nathanjds001/fdspapr/src/cad_pictures/Filter Cap.jpg

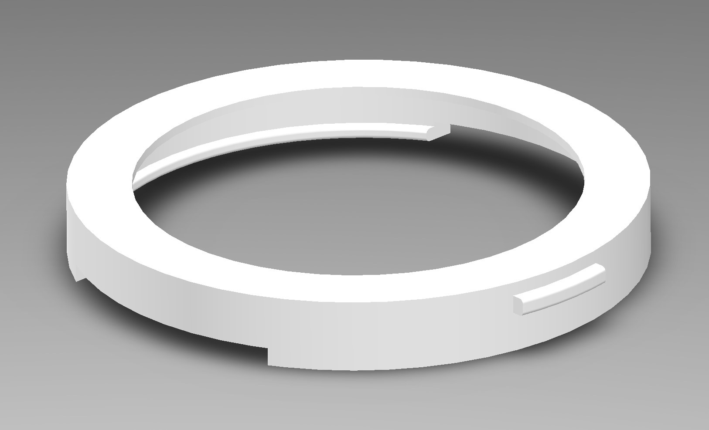
src/cad_pictures/Filter Cap.jpg
