nathanjds001/fdspapr/src/cad_pictures/Filter ring.jpg

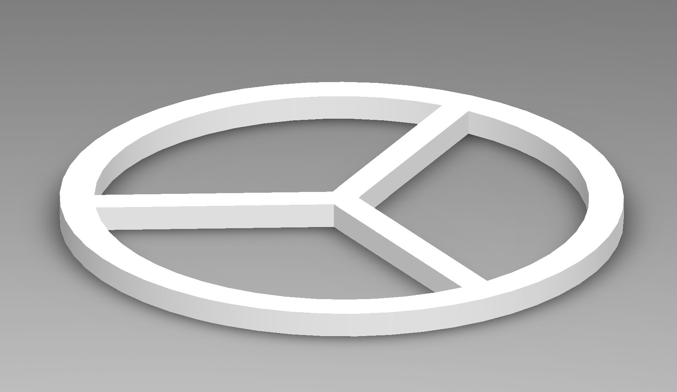
src/cad_pictures/Filter ring.jpg
