nathanjds001/fdspapr/src/cad_pictures/Housing.jpg

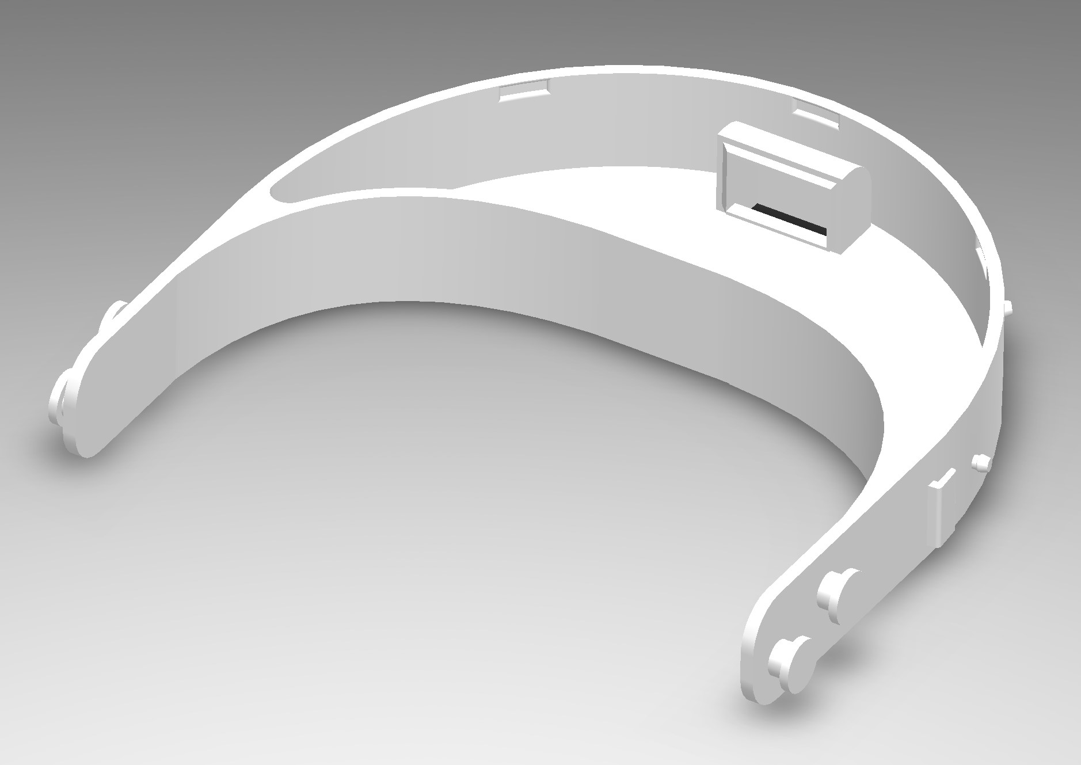
src/cad_pictures/Housing.jpg
