nathanjds001/fdspapr/src/cad_pictures/Lid.jpg

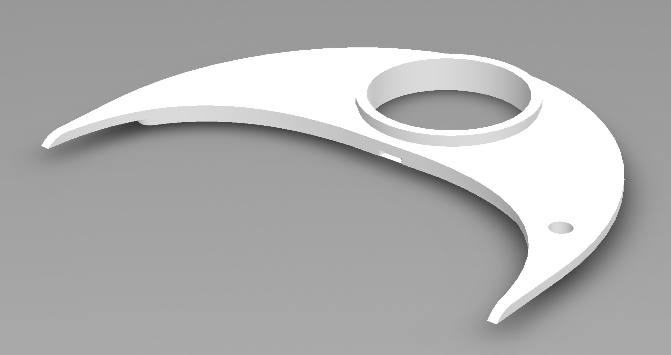
src/cad_pictures/Lid.jpg
