nathanjds001/fdspapr/src/cad_pictures/Vent bottom.jpg

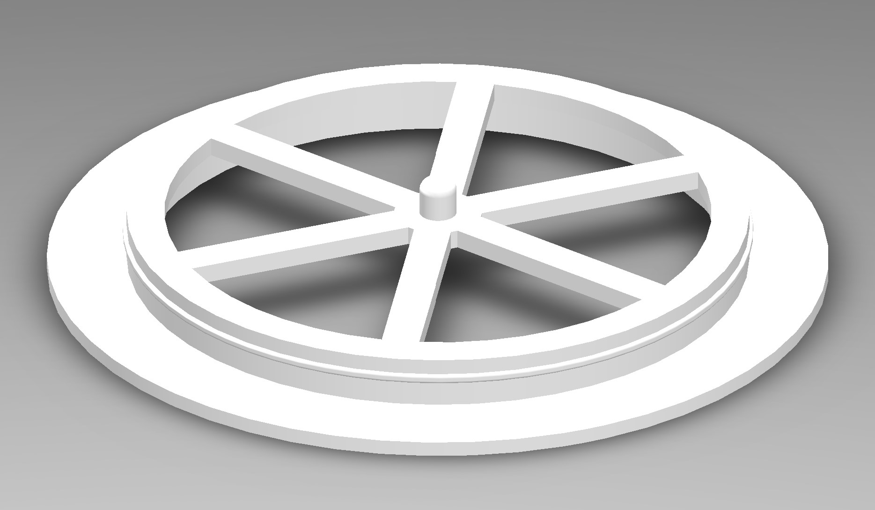
src/cad_pictures/Vent bottom.jpg
