nathanjds001/fdspapr/src/cad_pictures/Vent top.jpg

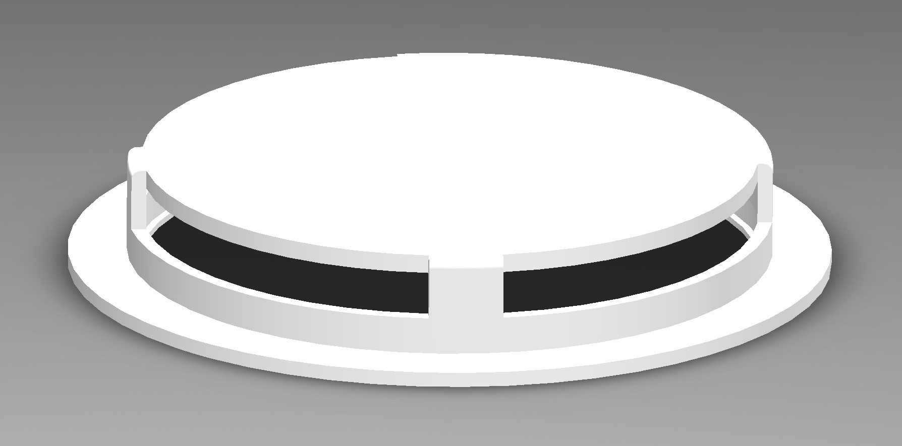
src/cad_pictures/Vent top.jpg
