nathanjds001/fdspapr/src/instructables_pictures/0.3 Components - Labelled.png

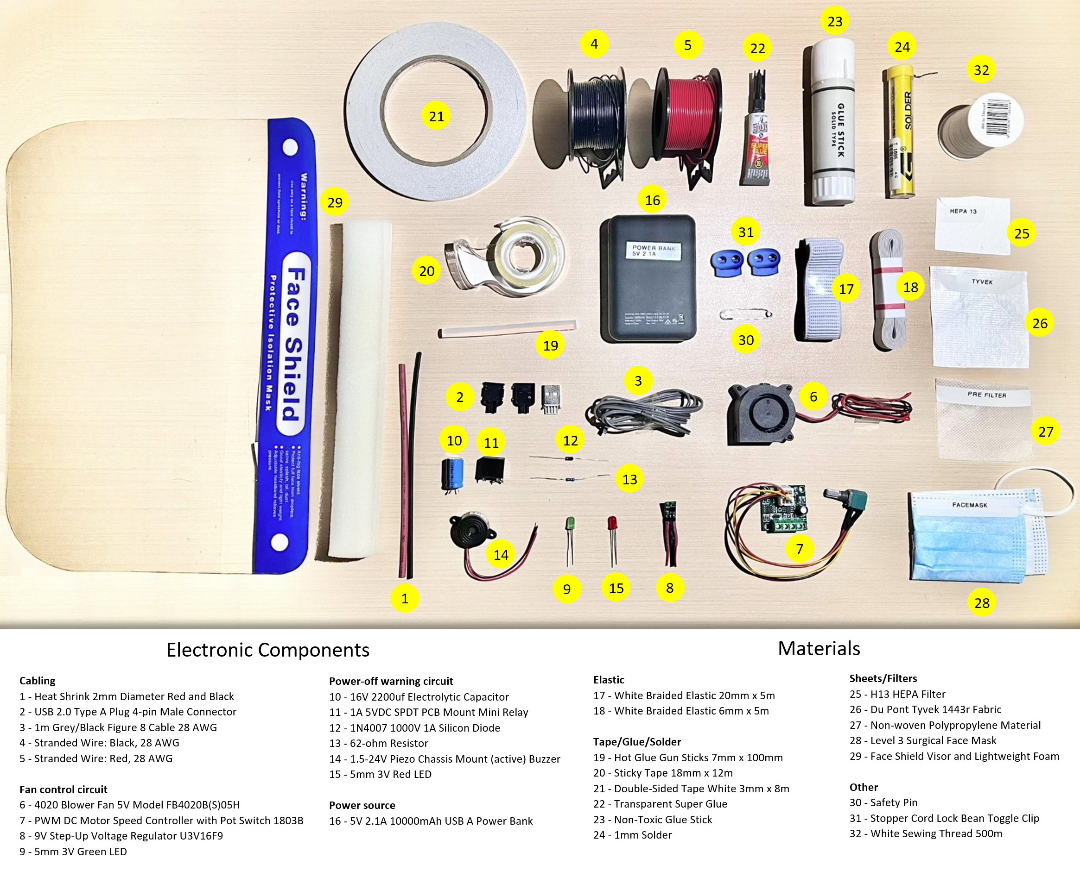
src/instructables_pictures/0.3 Components - Labelled.png
