nathanjds001/fdspapr/src/instructables_pictures/0.3 Components.jpg

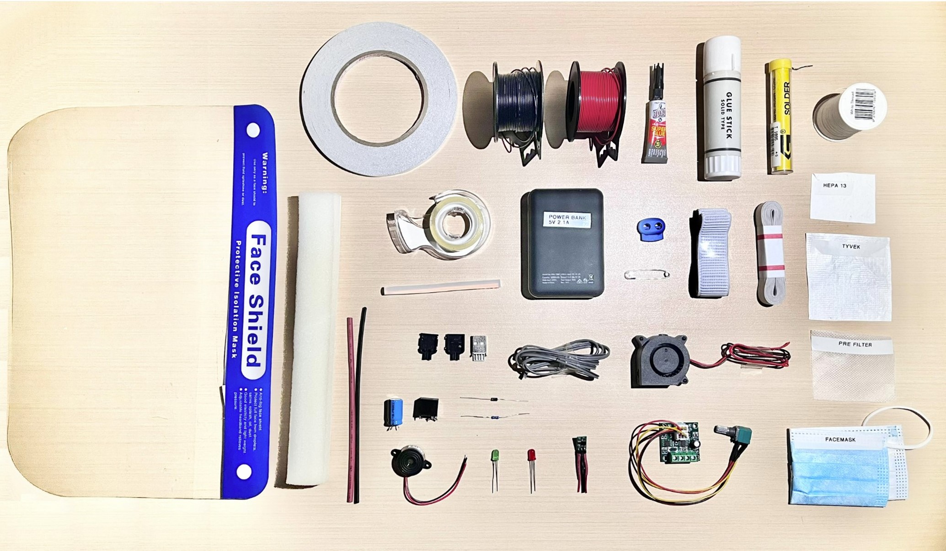
src/instructables_pictures/0.3 Components.jpg
