nathanjds001/fdspapr/src/instructables_pictures/1.2 3D Parts.jpg

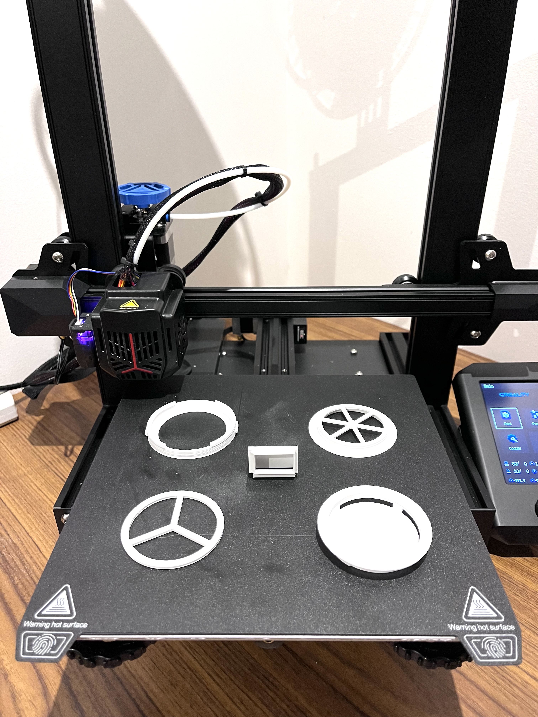
src/instructables_pictures/1.2 3D Parts.jpg
