nathanjds001/fdspapr/src/cad/Solidworks_Files/1. Face Shield Assembly.SLDASM

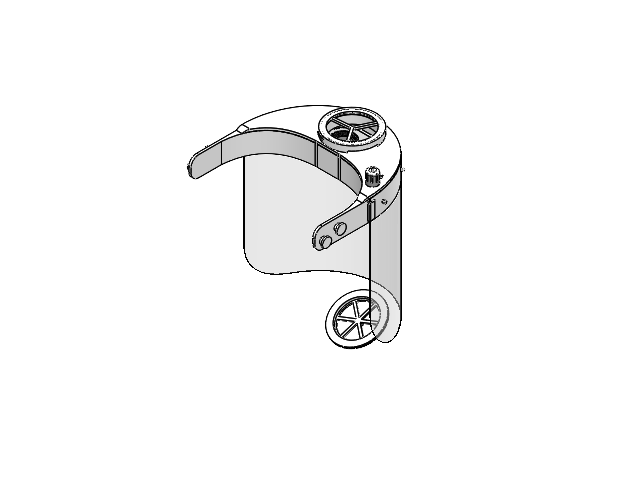
[picture p82: CAD file, 2024-04-08]
src/cad/Solidworks_Files/1. Face Shield Assembly.SLDASM
Vent bottom
Vent top
Housing
Plastic Shield
Lid
LED_D5.0mm_CLEAR x 2
4020 Blower Fan
Filter cap
Filter ring
Pot
4020 Blower Fan Funnel
Pot knob
