nathanjds001/fdspapr/src/cad_pictures/Assembly exploded view screenshot.jpg

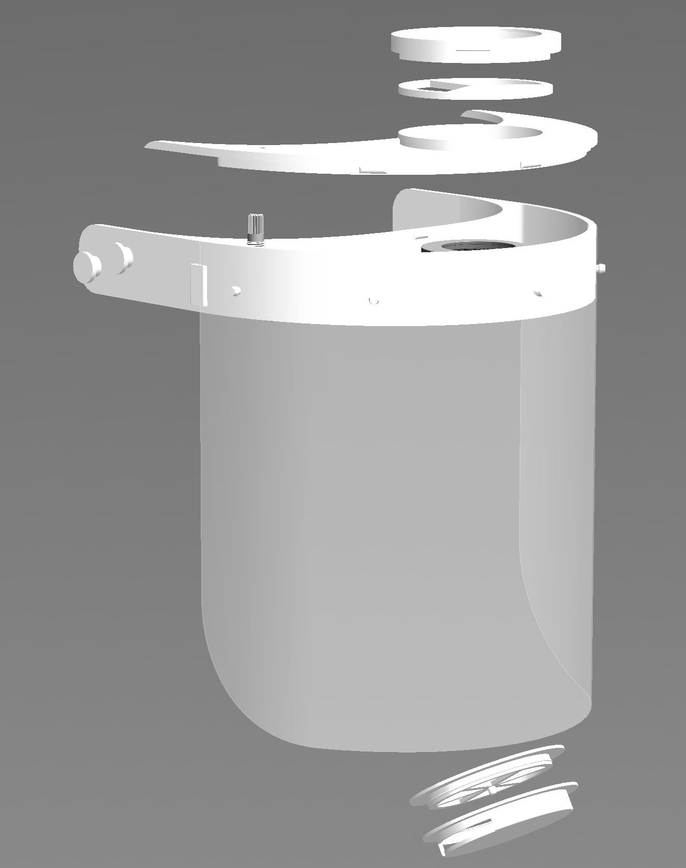
src/cad_pictures/Assembly exploded view screenshot.jpg
