nathanjds001/fdspapr/src/cad_pictures/Assembly Screenshot white bg 2.jpg

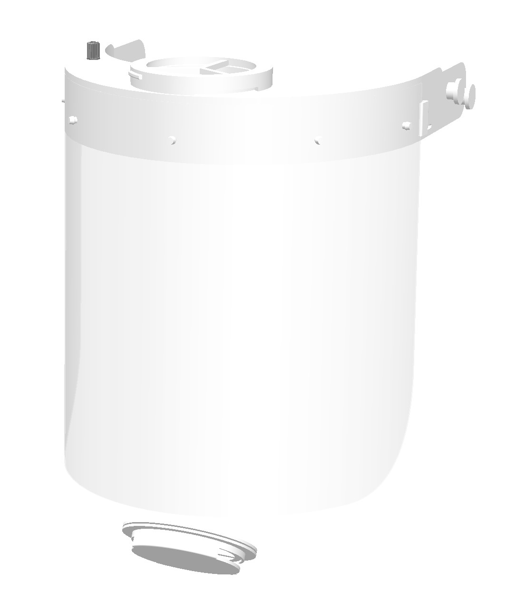
src/cad_pictures/Assembly Screenshot white bg 2.jpg
