nathanjds001/fdspapr/src/cad_pictures/Assembly Screenshot white bg.jpg

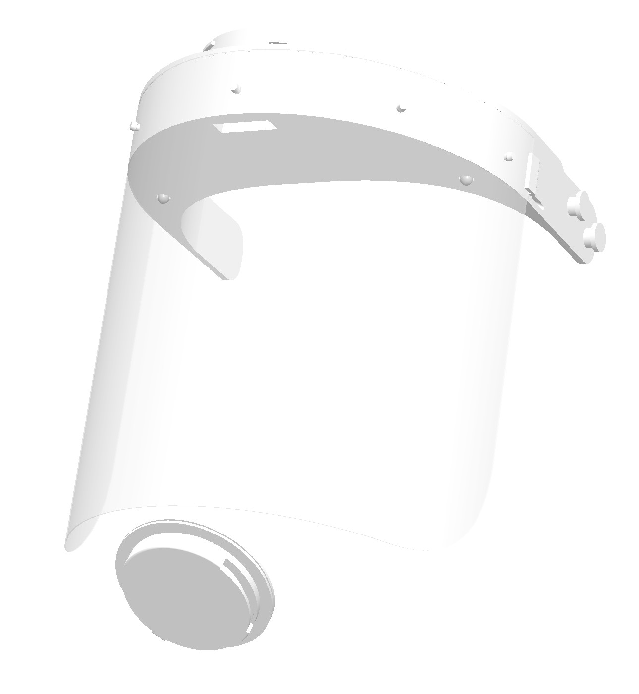
src/cad_pictures/Assembly Screenshot white bg.jpg
