nathanjds001/fdspapr/src/cad_pictures/Assembly screenshot.jpg

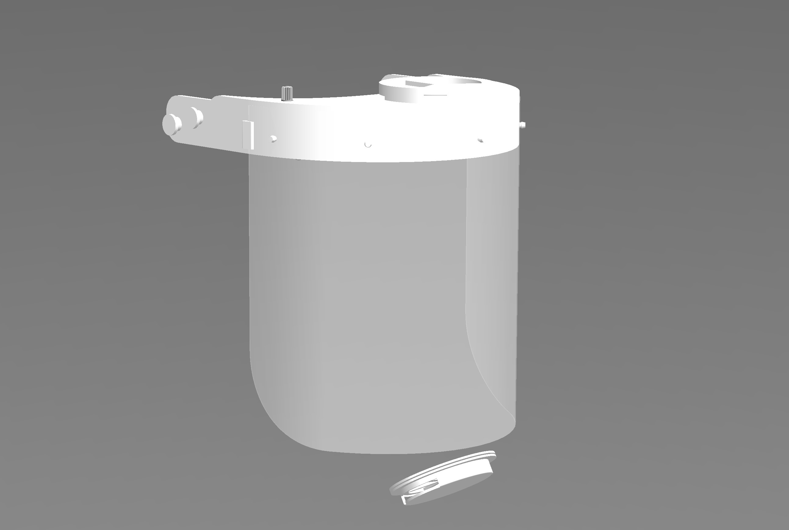
src/cad_pictures/Assembly screenshot.jpg
