nathanjds001/fdspapr/src/instructables_pictures/0.1 Full PAPR.png

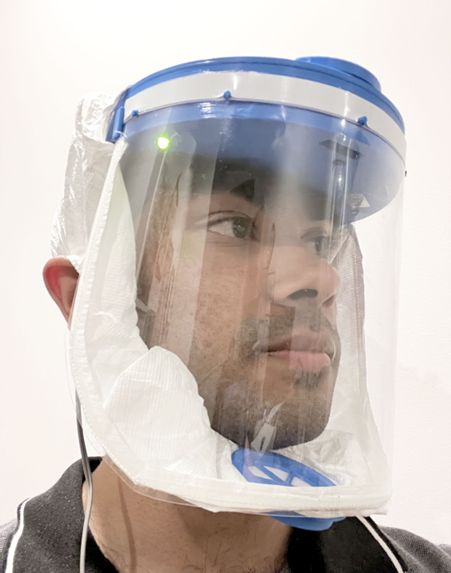
src/instructables_pictures/0.1 Full PAPR.png
