nathanjds001/fdspapr/src/instructables_pictures/0.2 Simple PAPR.jpg

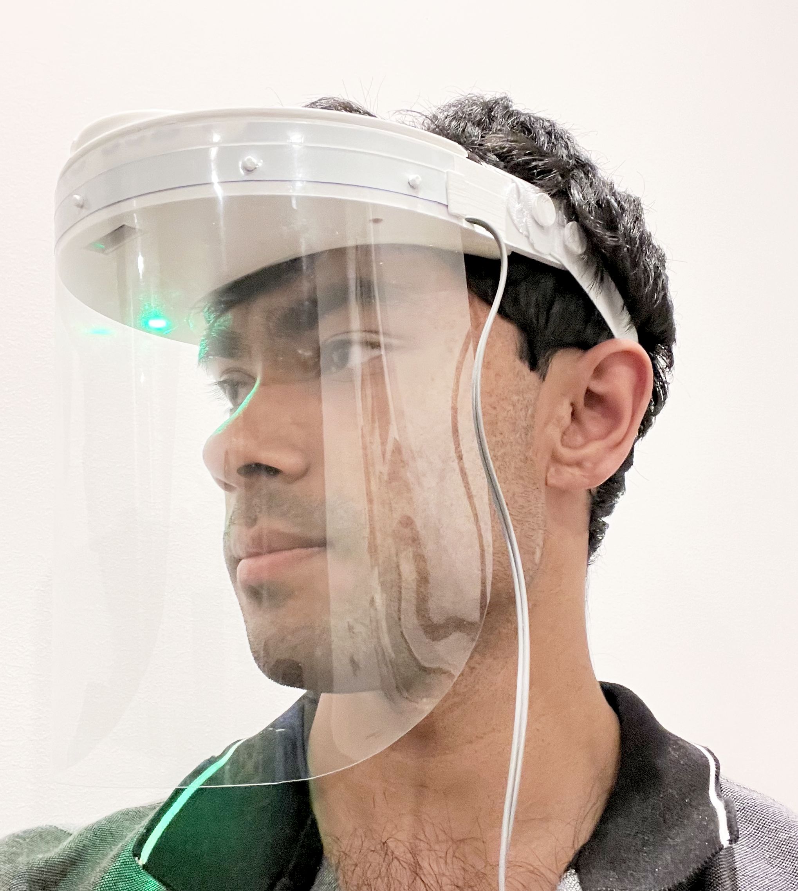
src/instructables_pictures/0.2 Simple PAPR.jpg
