nathanjds001/fdspapr/src/instructables_pictures/2.1 Fan Control Circuit.jpg

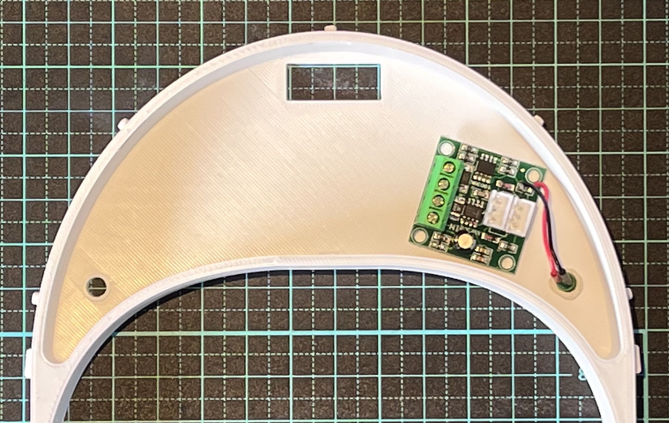
src/instructables_pictures/2.1 Fan Control Circuit.jpg
