nathanjds001/fdspapr/src/instructables_pictures/2.2 Fan Control Circuit.jpg

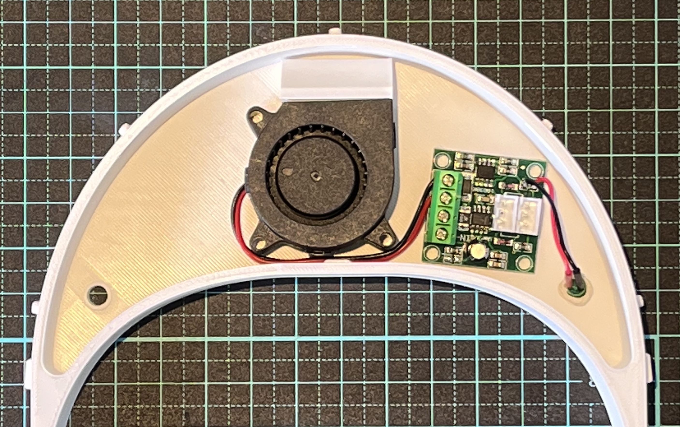
src/instructables_pictures/2.2 Fan Control Circuit.jpg
