nathanjds001/fdspapr/src/instructables_pictures/2.5 Power Off Warning Circuit - Labelled.png

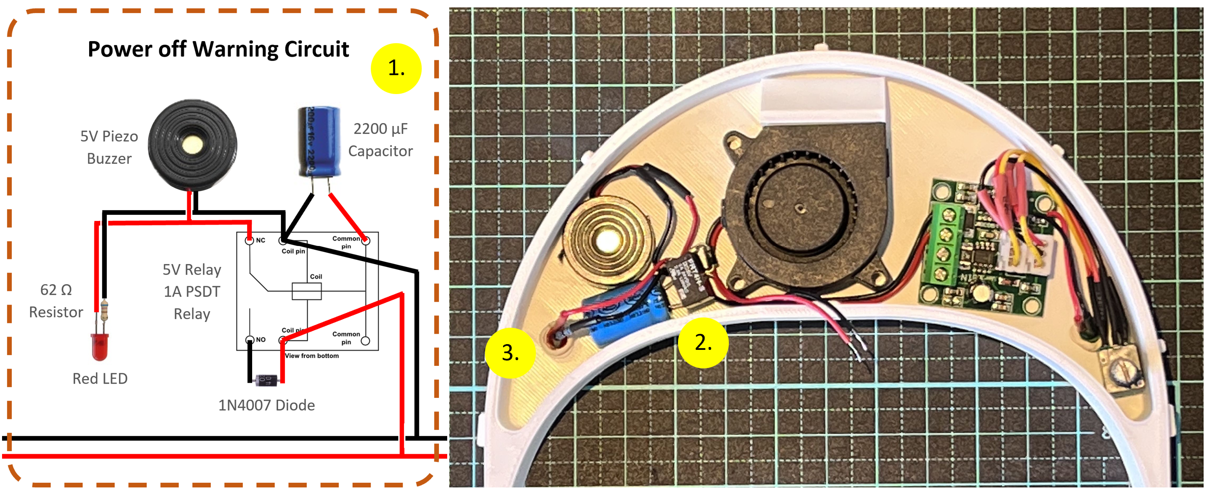
src/instructables_pictures/2.5 Power Off Warning Circuit - Labelled.png
