nathanjds001/fdspapr/src/instructables_pictures/2.6 Power Connections.jpg

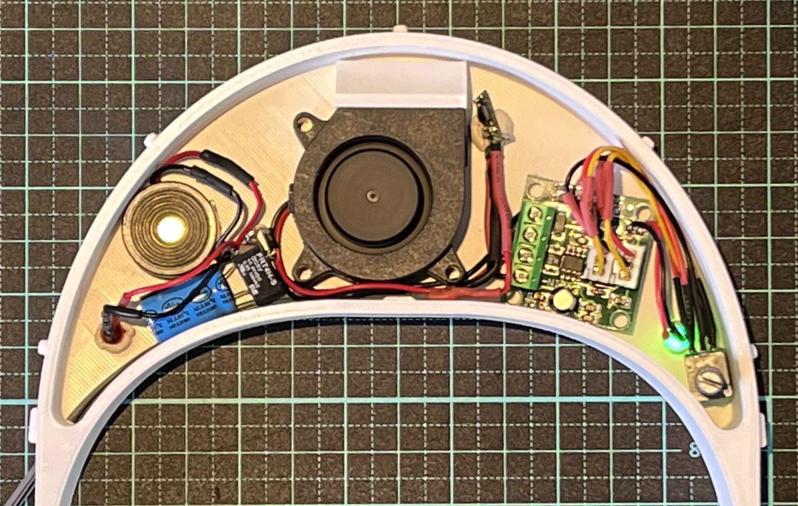
src/instructables_pictures/2.6 Power Connections.jpg
