nathanjds001/fdspapr/src/instructables_pictures/2.7 Close Lid.jpg

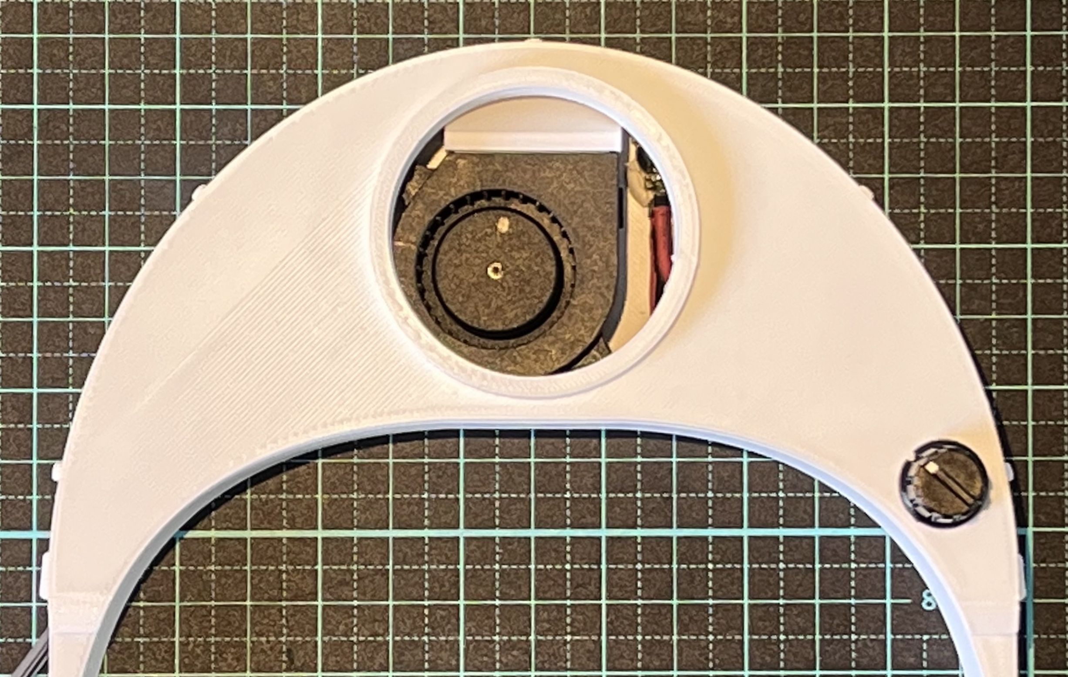
src/instructables_pictures/2.7 Close Lid.jpg
