nathanjds001/fdspapr/src/instructables_pictures/3.2 Inlet Filter Fixed.jpg

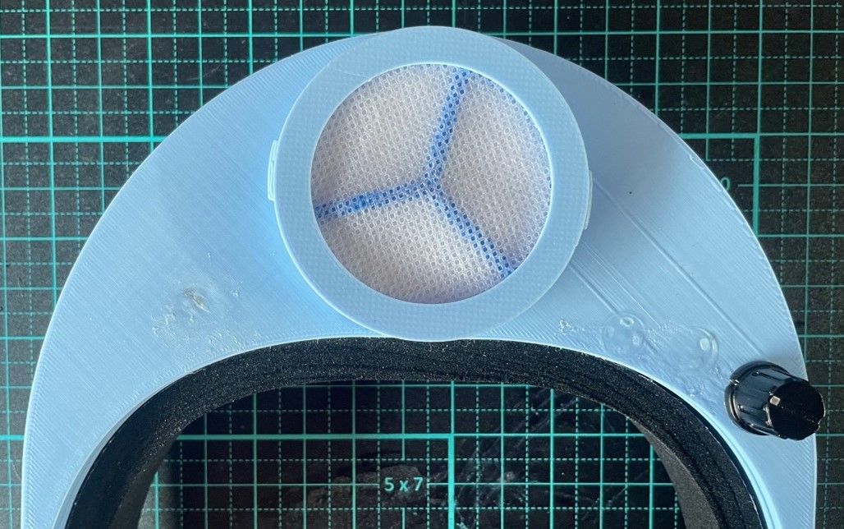
src/instructables_pictures/3.2 Inlet Filter Fixed.jpg
