nathanjds001/fdspapr/src/instructables_pictures/4.1 Foam.jpg

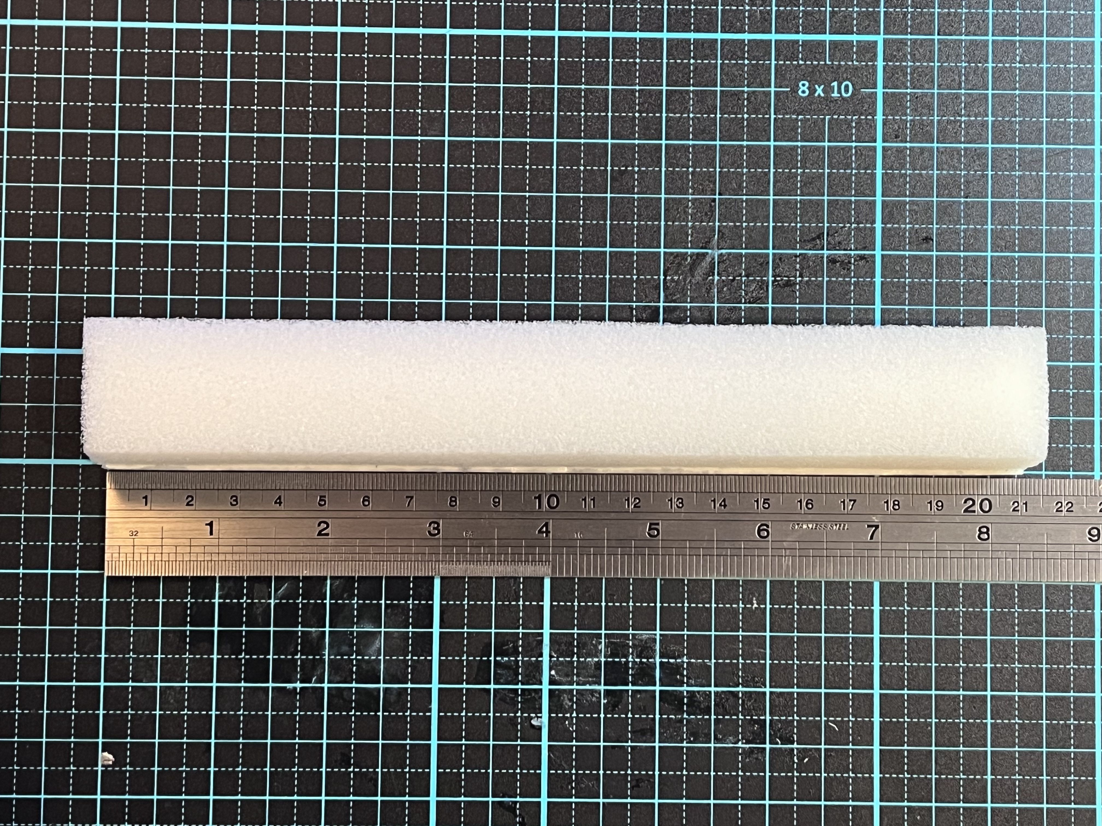
src/instructables_pictures/4.1 Foam.jpg
