nathanjds001/fdspapr/src/instructables_pictures/5.1 Headstrap.jpg

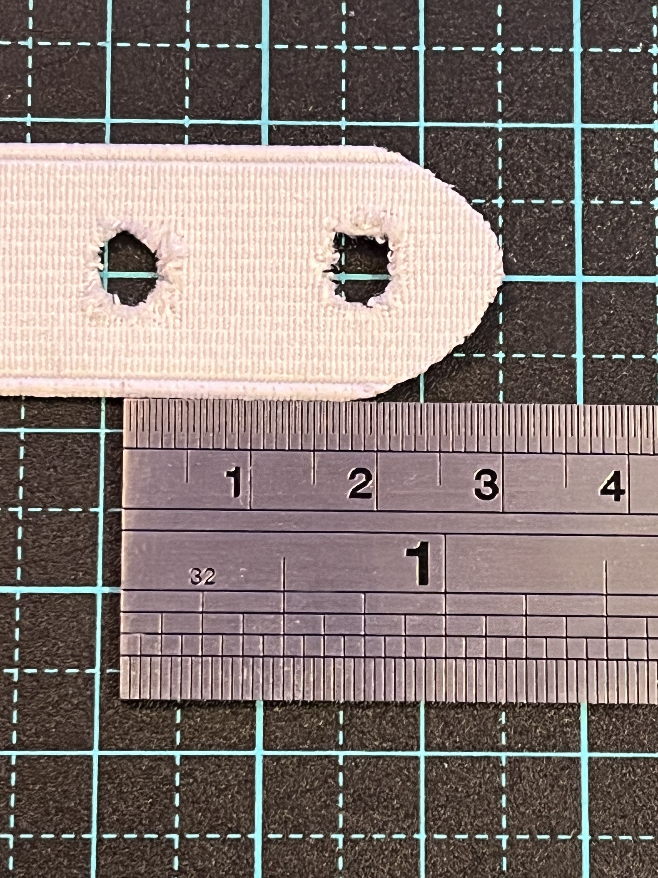
src/instructables_pictures/5.1 Headstrap.jpg
