nathanjds001/fdspapr/src/instructables_pictures/5.2 Headstrap.jpg

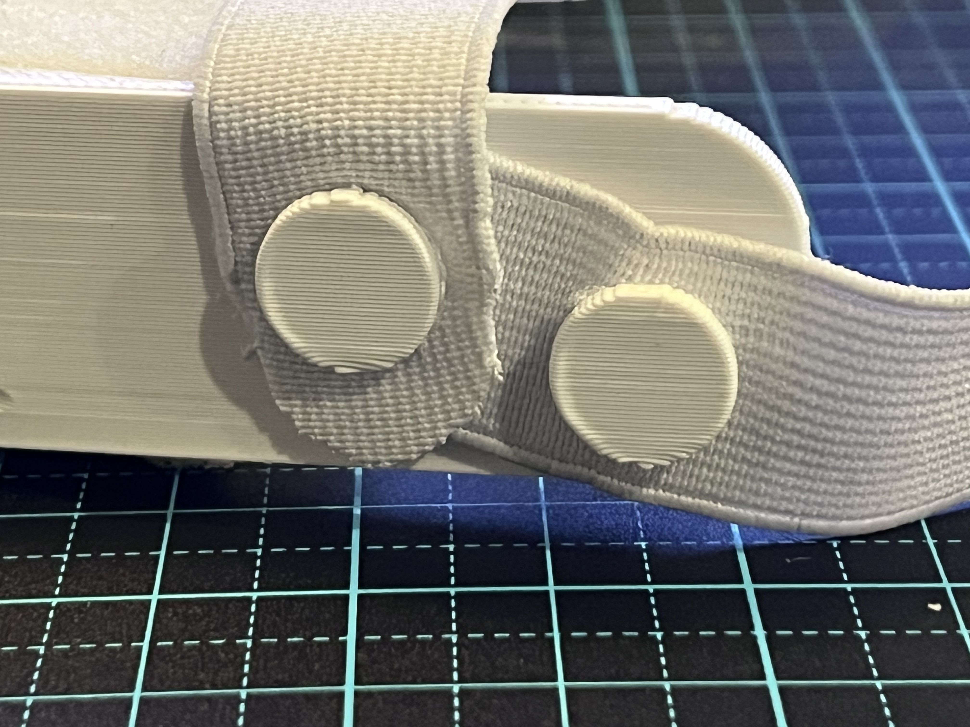
src/instructables_pictures/5.2 Headstrap.jpg
