nathanjds001/fdspapr/src/instructables_pictures/5.3 Headstrap.jpg

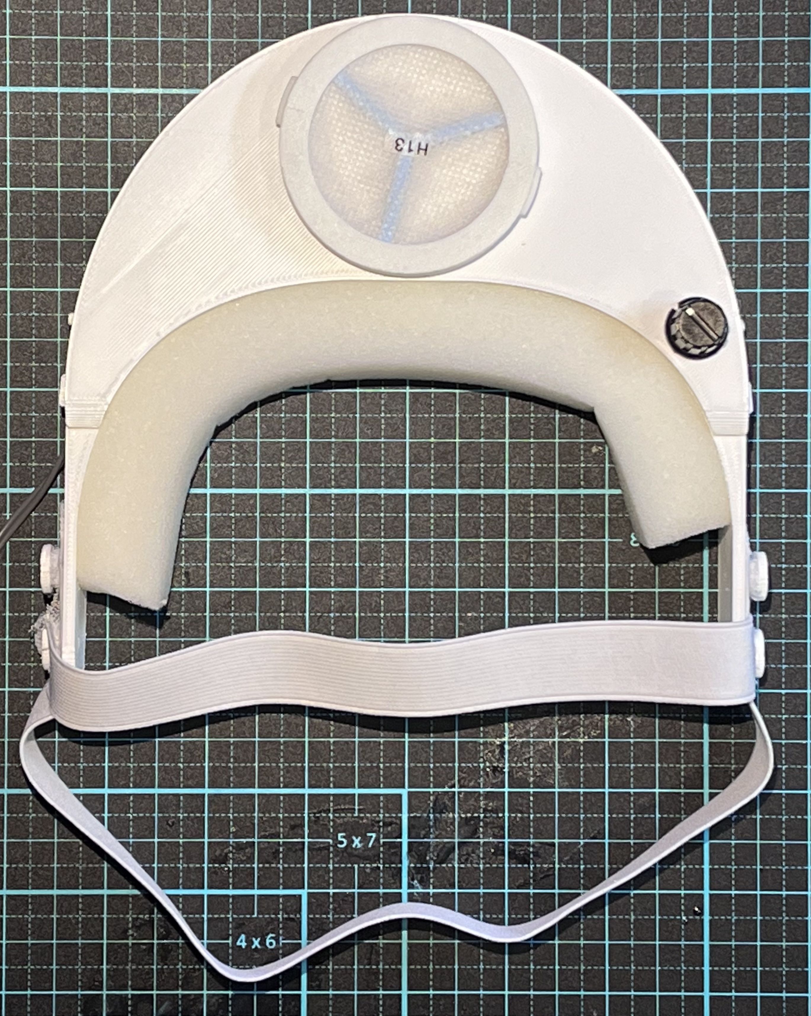
src/instructables_pictures/5.3 Headstrap.jpg
