nathanjds001/fdspapr/src/instructables_pictures/6.1 Visor.jpg

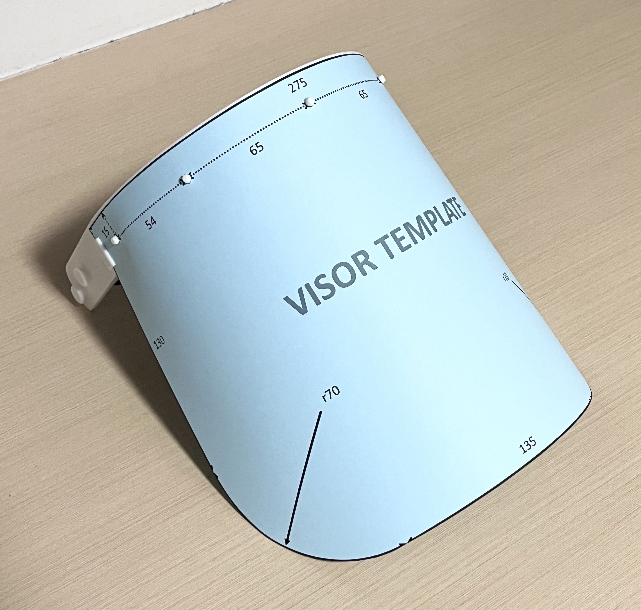
src/instructables_pictures/6.1 Visor.jpg
