nathanjds001/fdspapr/src/instructables_pictures/6.2 Visor.jpg

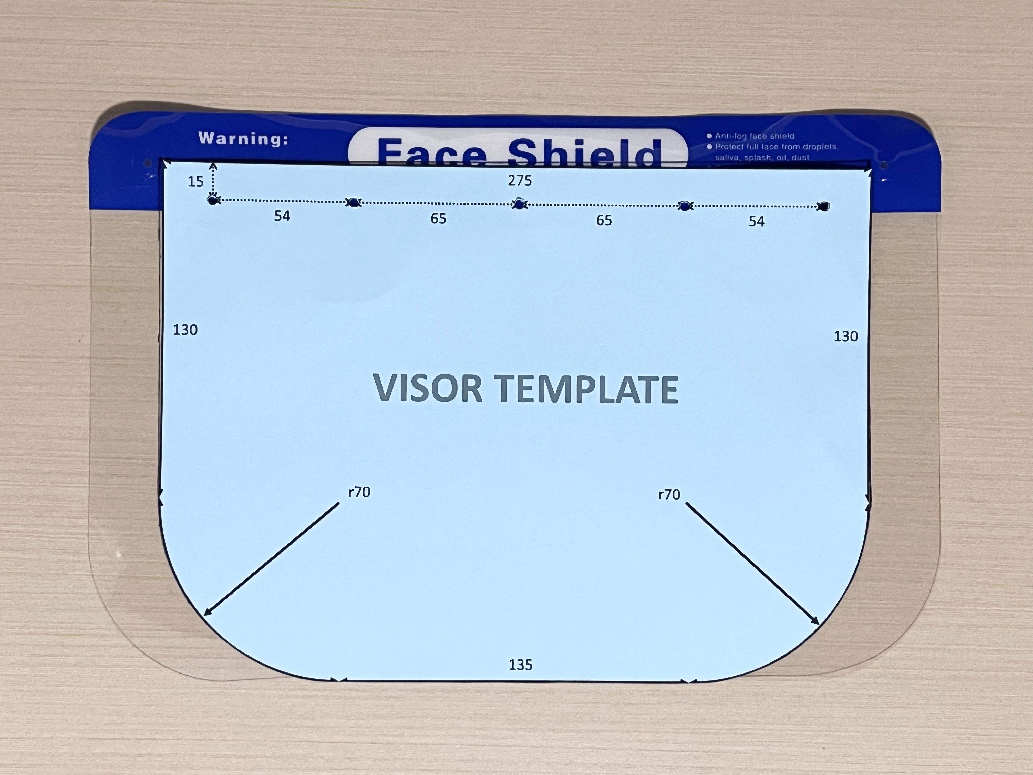
src/instructables_pictures/6.2 Visor.jpg
