nathanjds001/fdspapr/src/instructables_pictures/6.4 Visor.jpg

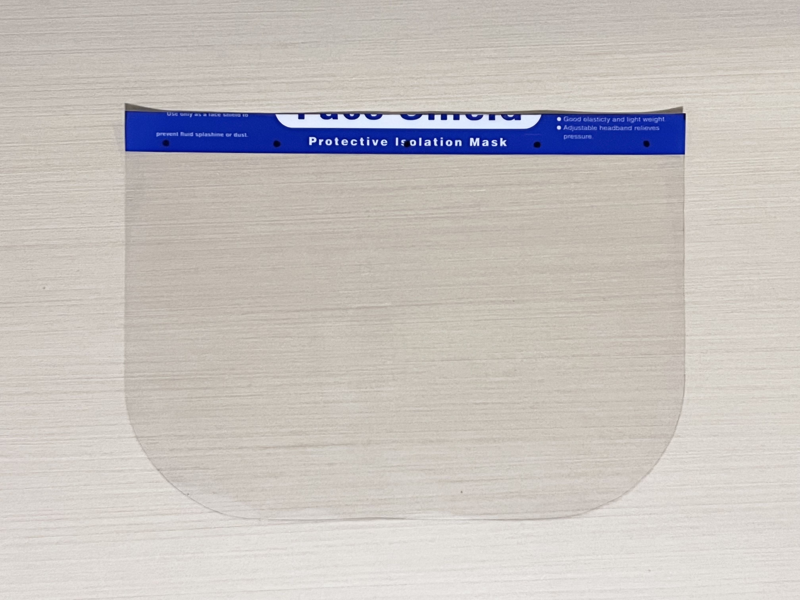
src/instructables_pictures/6.4 Visor.jpg
