nathanjds001/fdspapr/src/instructables_pictures/6.5 Visor.jpg

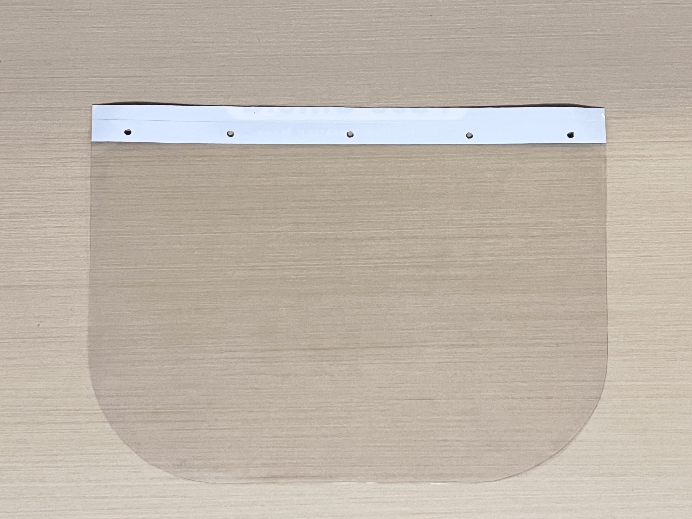
src/instructables_pictures/6.5 Visor.jpg
