nathanjds001/fdspapr/src/instructables_pictures/6.6 Visor.jpg

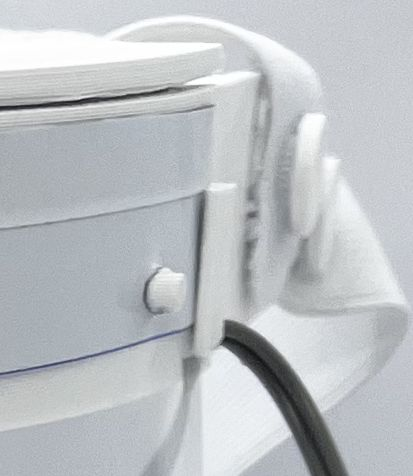
src/instructables_pictures/6.6 Visor.jpg
