nathanjds001/fdspapr/src/instructables_pictures/6.7 Visor.jpg

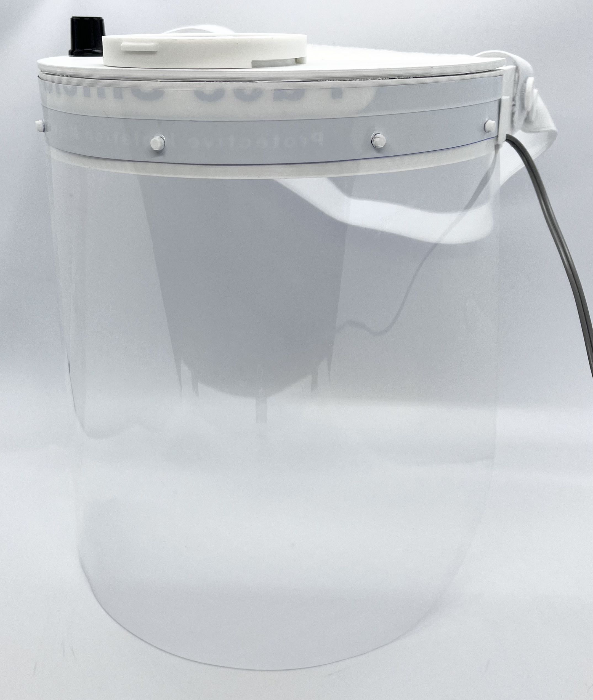
src/instructables_pictures/6.7 Visor.jpg
