nathanjds001/fdspapr/src/instructables_pictures/7.1 Hood Template.jpg

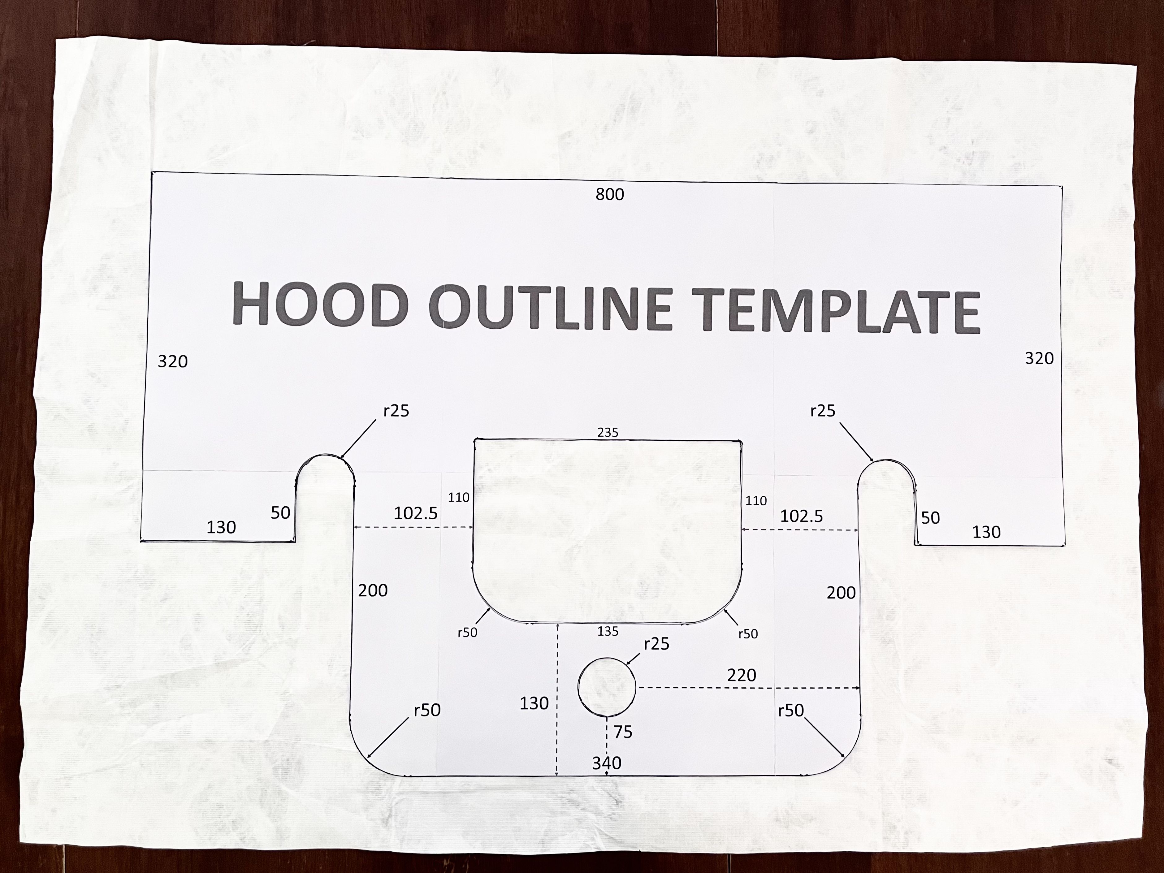
src/instructables_pictures/7.1 Hood Template.jpg
