nathanjds001/fdspapr/src/instructables_pictures/8.1 Hood folds.png

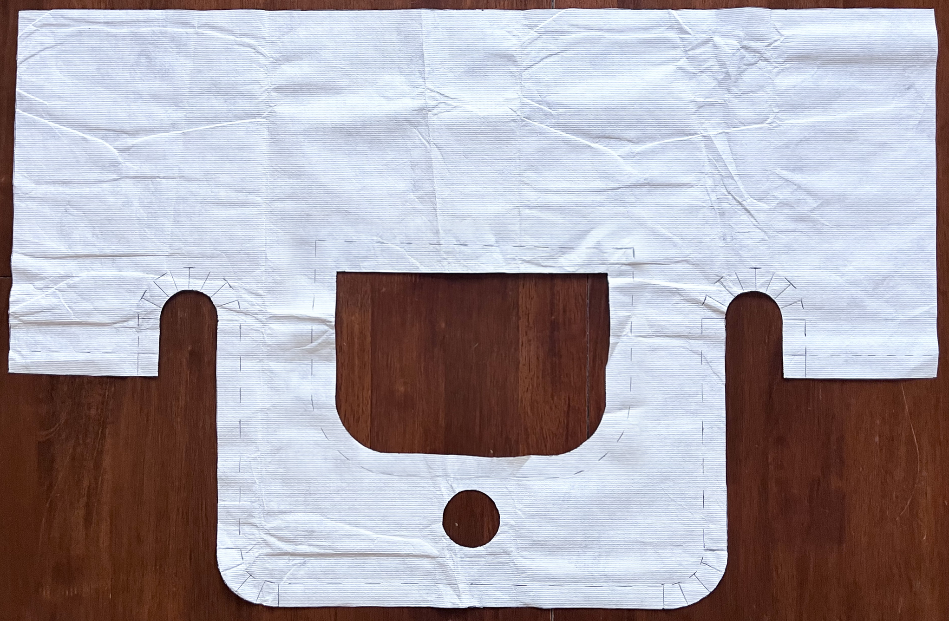
src/instructables_pictures/8.1 Hood folds.png
