nathanjds001/fdspapr/src/instructables_pictures/9.1 Arch.jpg

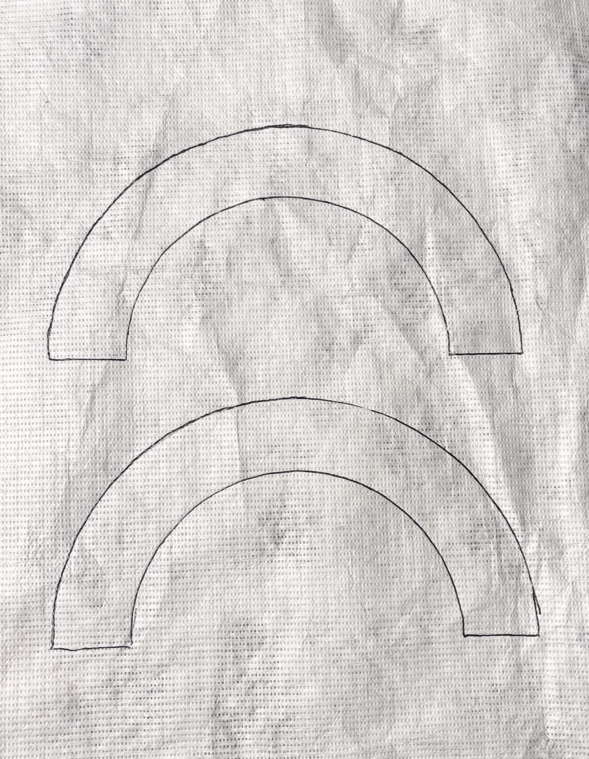
src/instructables_pictures/9.1 Arch.jpg
