nathanjds001/fdspapr/src/instructables_pictures/9.2 Arch.jpg

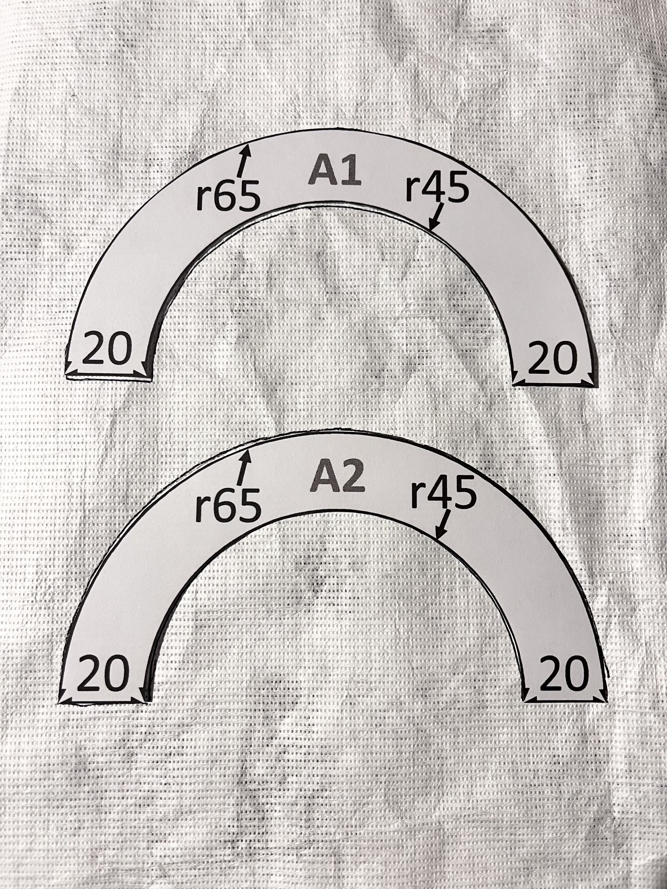
src/instructables_pictures/9.2 Arch.jpg
