nathanjds001/fdspapr/src/instructables_pictures/9.3 Arch.jpg

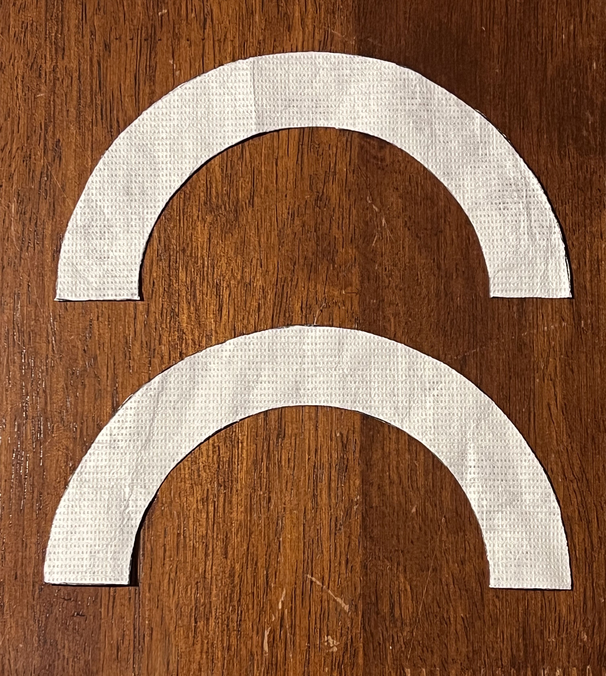
src/instructables_pictures/9.3 Arch.jpg
