nathanjds001/fdspapr/src/instructables_pictures/9.4 Arch.jpg

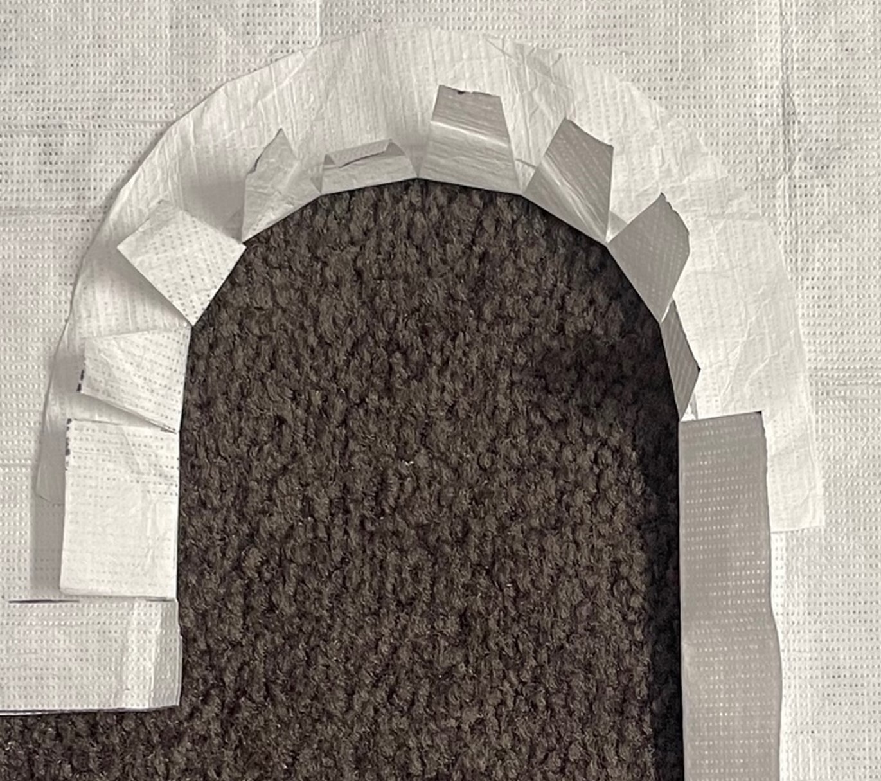
src/instructables_pictures/9.4 Arch.jpg
