nathanjds001/fdspapr/src/instructables_pictures/9.5 Arch.jpg

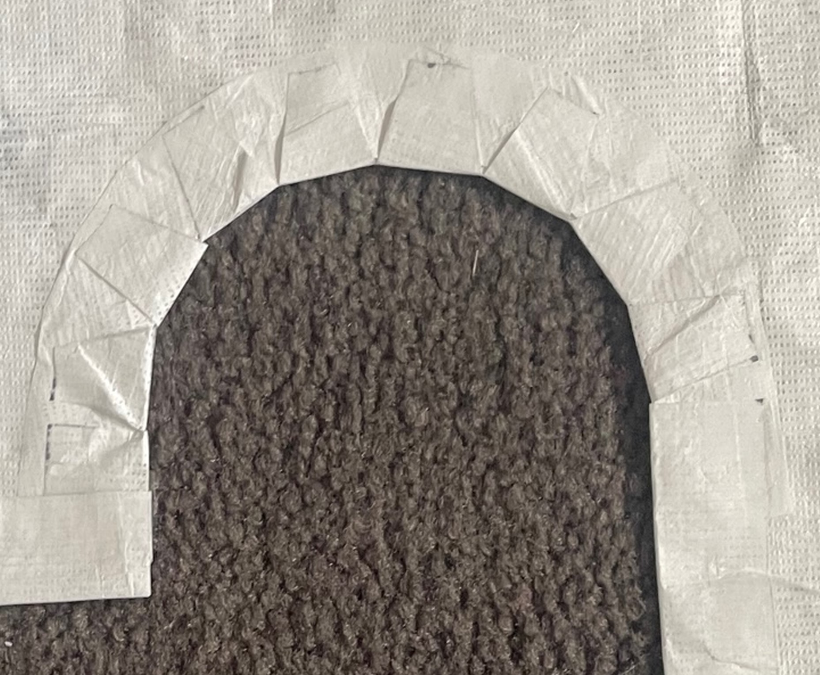
src/instructables_pictures/9.5 Arch.jpg
