nathanjds001/fdspapr/src/instructables_pictures/10.1 Visor to Hood.jpg

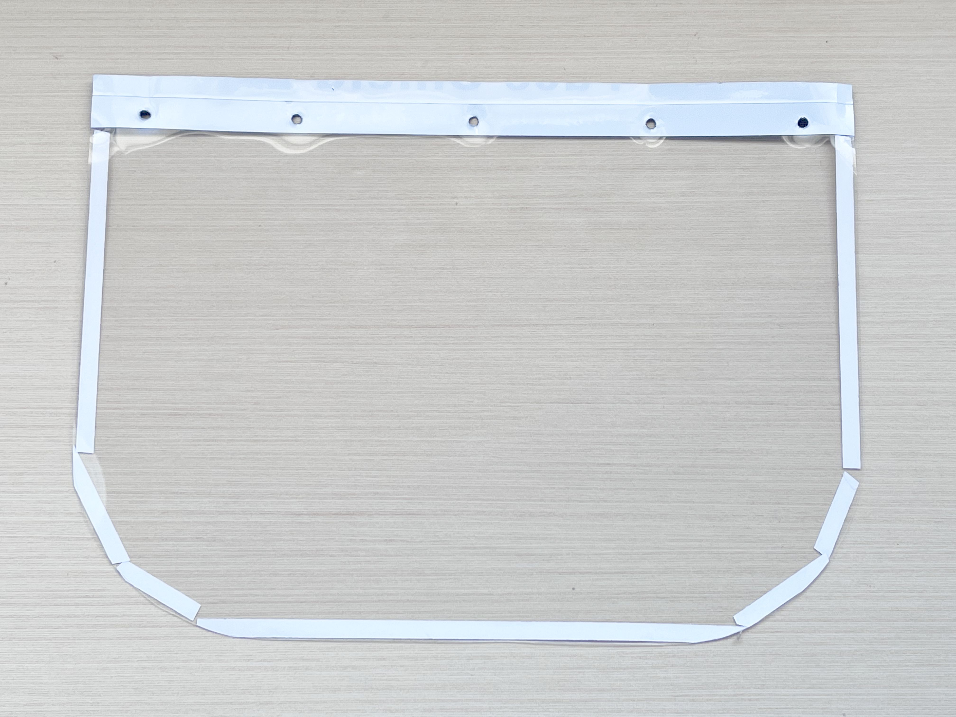
src/instructables_pictures/10.1 Visor to Hood.jpg
