nathanjds001/fdspapr/src/instructables_pictures/11.5 Stitch Folds and Visor.jpg

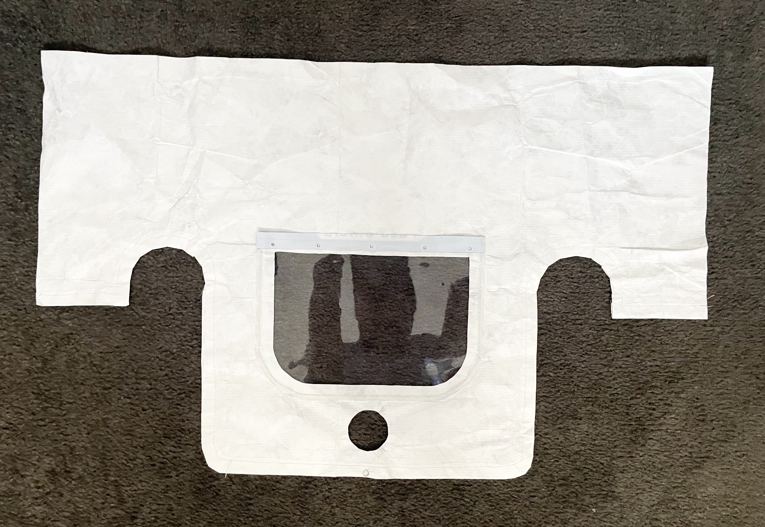
src/instructables_pictures/11.5 Stitch Folds and Visor.jpg
