nathanjds001/fdspapr/src/instructables_pictures/12.1 Thread Elastic.jpg

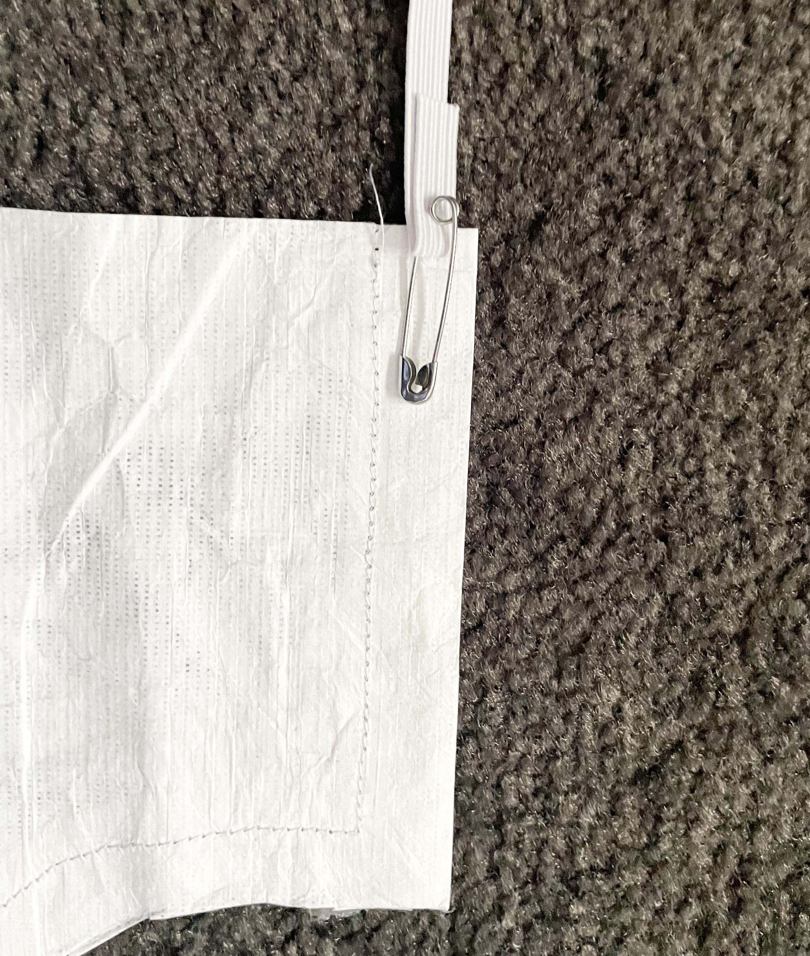
src/instructables_pictures/12.1 Thread Elastic.jpg
