nathanjds001/fdspapr/src/instructables_pictures/13.3 Outlet Filter.jpg

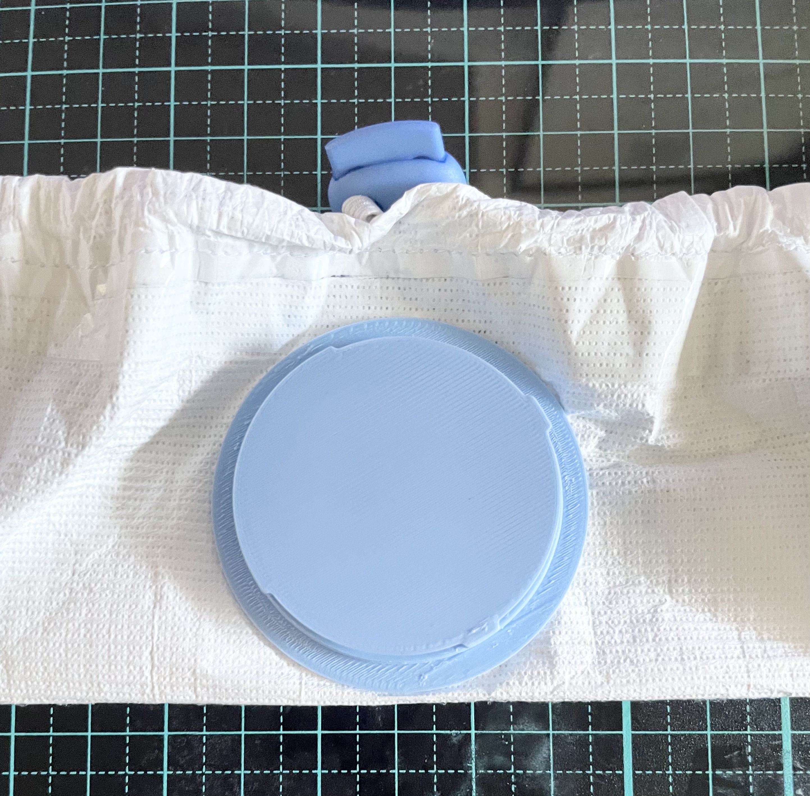
src/instructables_pictures/13.3 Outlet Filter.jpg
