nathanjds001/fdspapr/src/instructables_pictures/15.2 Bundle Top.jpg

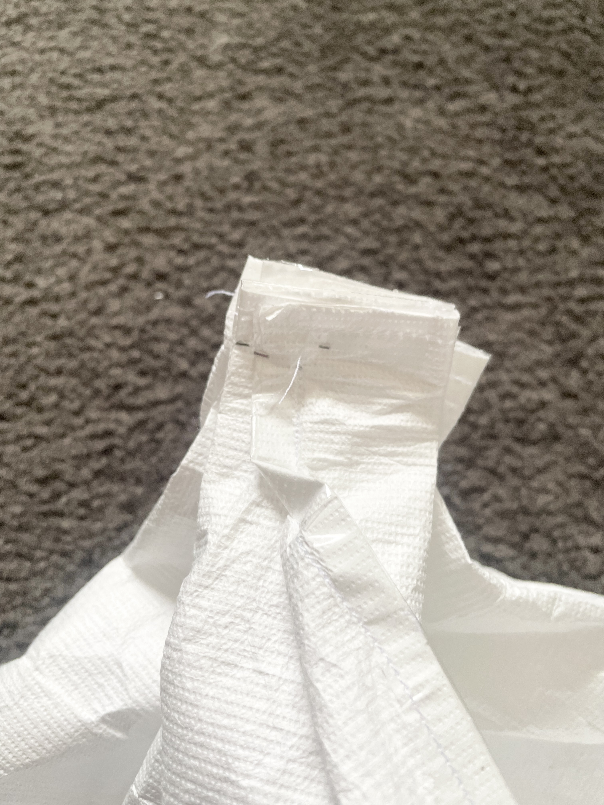
src/instructables_pictures/15.2 Bundle Top.jpg
