nathanjds001/fdspapr/src/instructables_pictures/15.3 Turn inside out.jpg

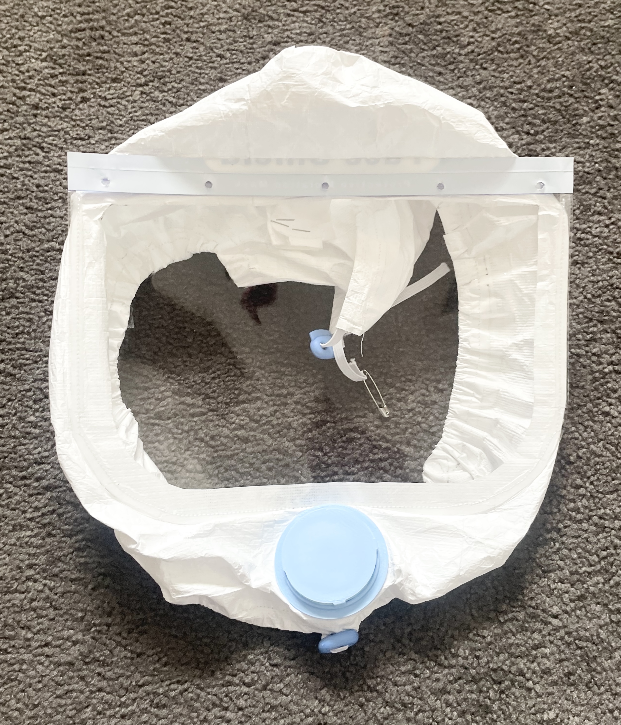
src/instructables_pictures/15.3 Turn inside out.jpg
