nathanjds001/fdspapr/src/instructables_pictures/15.4 Turn Inside out.jpg

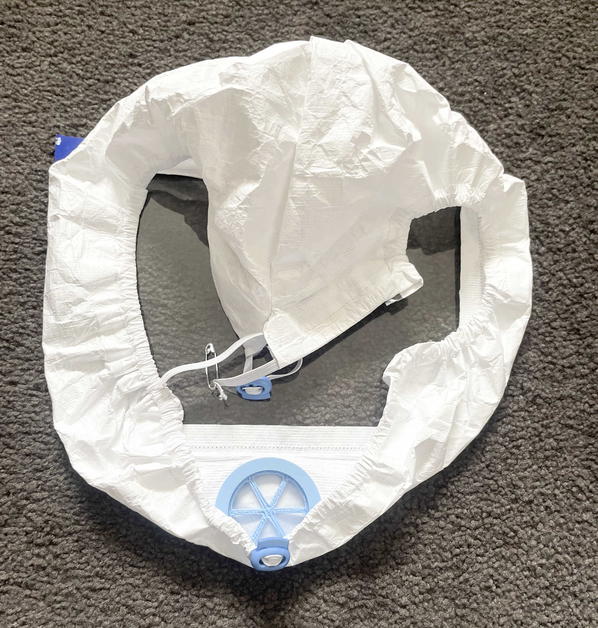
src/instructables_pictures/15.4 Turn Inside out.jpg
