nathanjds001/fdspapr/src/instructables_pictures/16.2 Hood to Housing.jpg

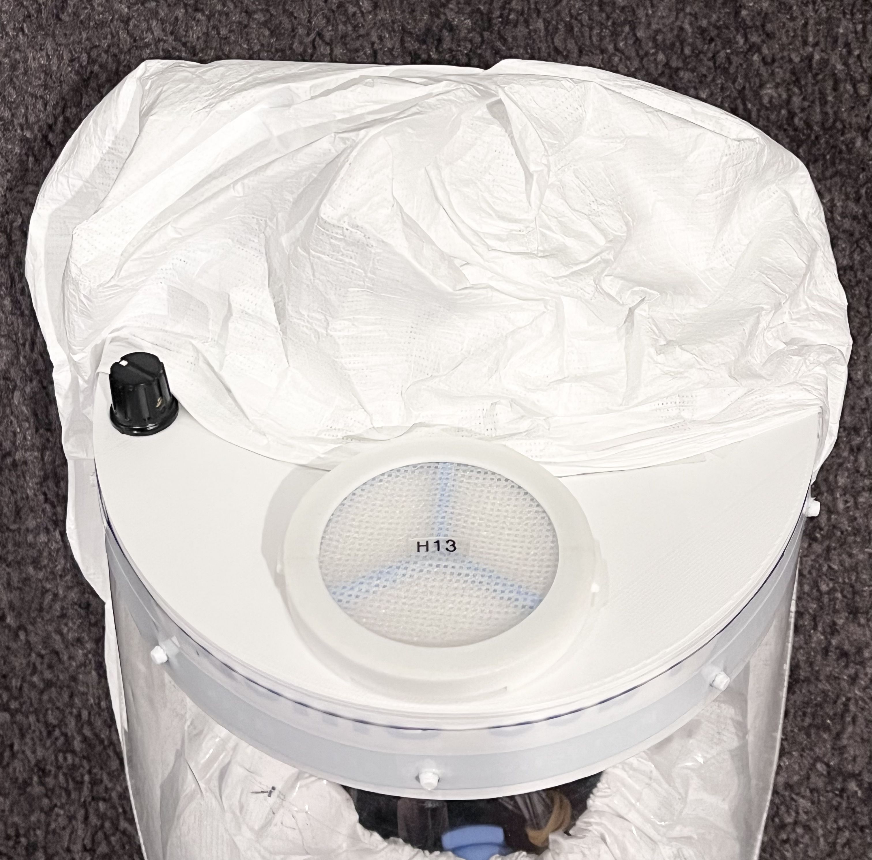
src/instructables_pictures/16.2 Hood to Housing.jpg
