nathanjds001/fdspapr/src/instructables_pictures/16.3 Hood to Housing.jpg

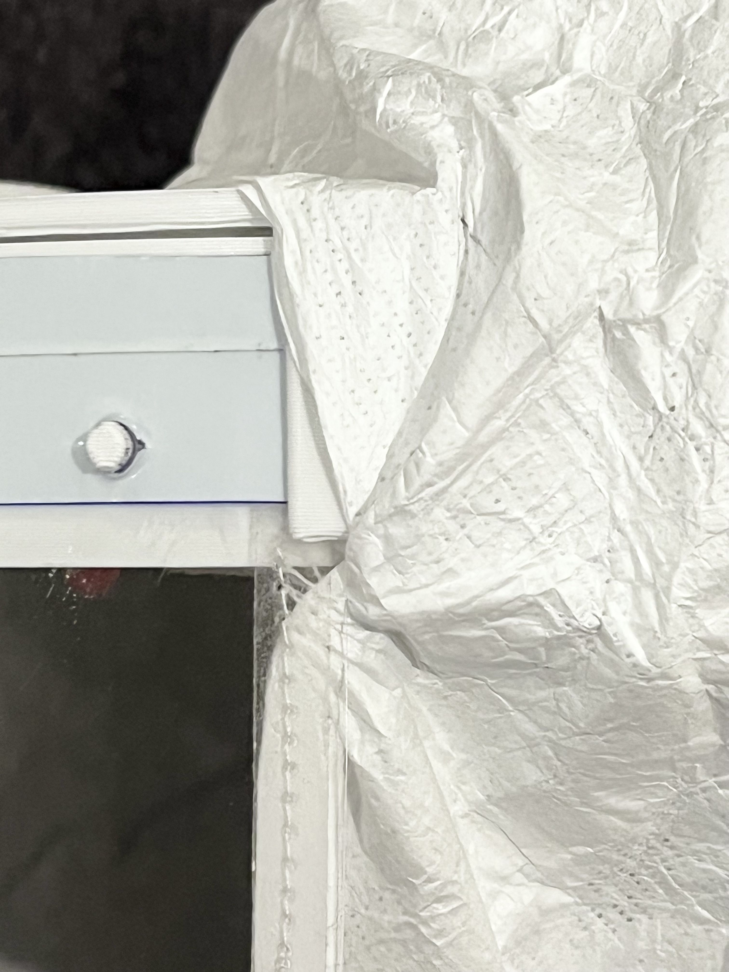
src/instructables_pictures/16.3 Hood to Housing.jpg
