nathanjds001/fdspapr/src/instructables_pictures/17.1 Hood Attached.jpg

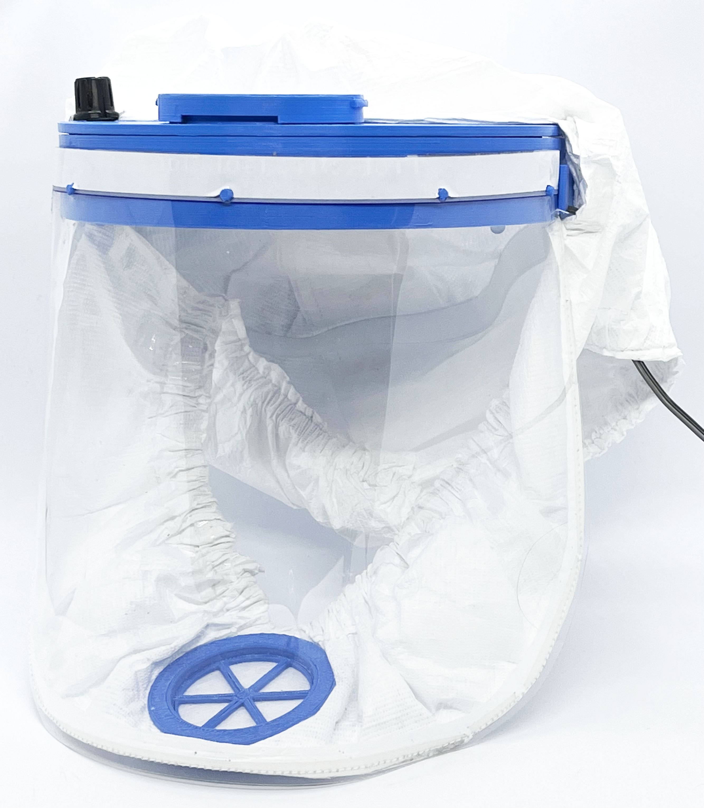
src/instructables_pictures/17.1 Hood Attached.jpg
